DoganM95/Jds-040-Usb-C/assets/IMG_20230802_171347.jpg

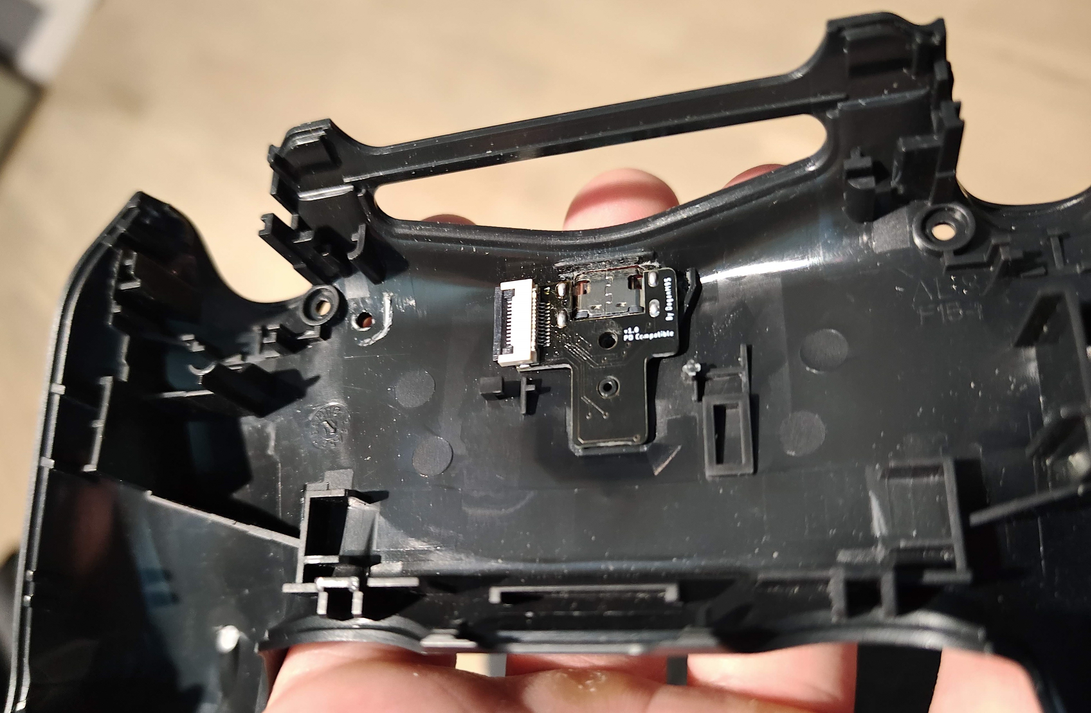
assets/IMG_20230802_171347.jpg
